WannaBAcoder/ArenaTimer/STLs/TimerPrints/Multi-Piece Housing/Bottom_right.stl

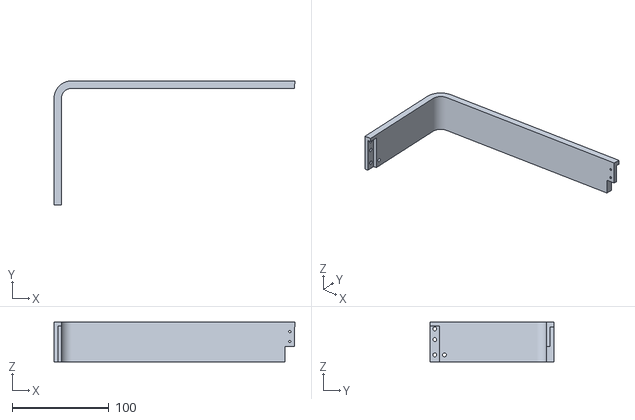
[picture p17: CAD file, 2026-06-10]
STLs/TimerPrints/Multi-Piece Housing/Bottom_right.stl
248.6 x 128.0 x 41.0
