WannaBAcoder/ArenaTimer/STLs/TimerPrints/Multi-Piece Housing/Lenses/seg_a.stl

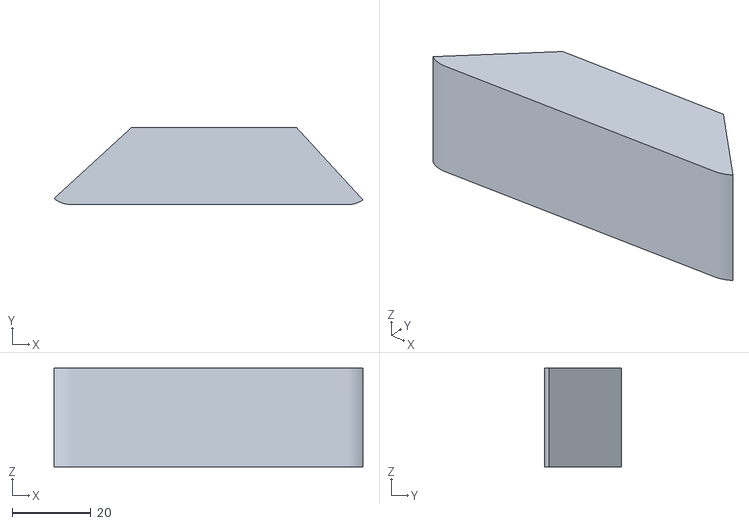
[picture p18: CAD file, 2026-06-10]
STLs/TimerPrints/Multi-Piece Housing/Lenses/seg_a.stl
78.4 x 19.6 x 25.0
