WannaBAcoder/ArenaTimer/STLs/TimerPrints/Single Piece Housing/Lenses/seg_a.stl

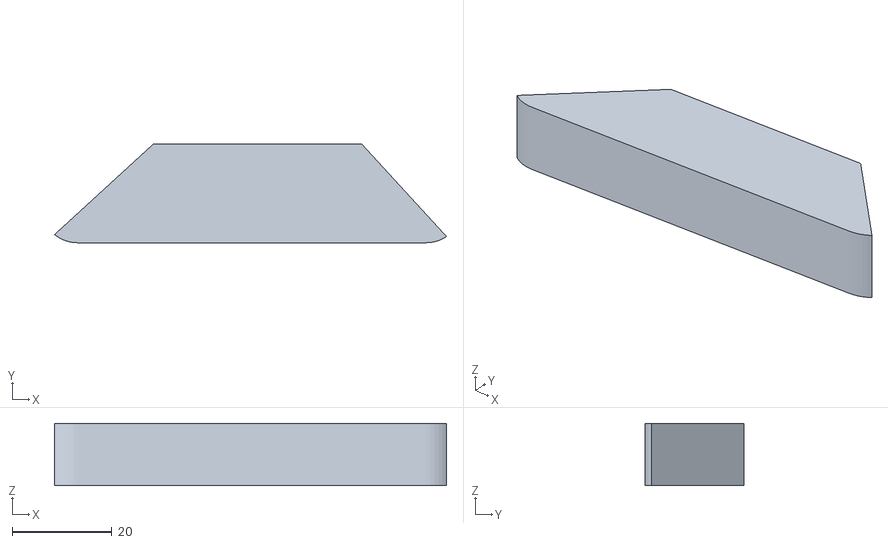
[picture p19: CAD file, 2026-06-10]
STLs/TimerPrints/Single Piece Housing/Lenses/seg_a.stl
78.7 x 19.8 x 12.5
