WannaBAcoder/ArenaTimer/STLs/TimerPrints/Button Cases/ControllerHousing/ControllerHousing_ButtonBoard v22_Body4.stl

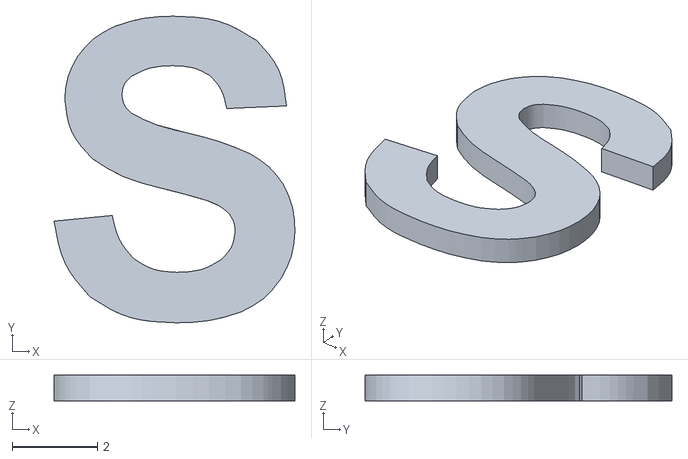
[picture p20: CAD file, 2026-06-10]
STLs/TimerPrints/Button Cases/ControllerHousing/ControllerHousing_ButtonBoard v22_Body4.stl
5.65 x 7.18 x 0.6
