WannaBAcoder/ArenaTimer/STLs/TimerPrints/Button Cases/ReadyButtonHousing/ReadyButtonHousing_LargerReadyButton v7_Body14.stl

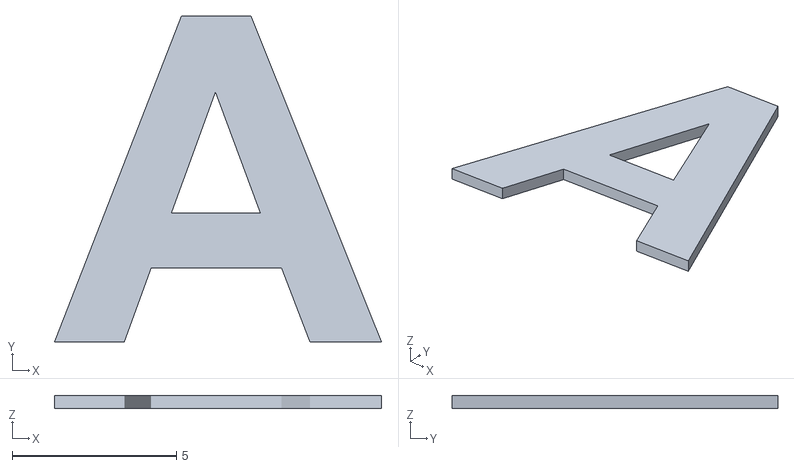
[picture p21: CAD file, 2026-06-10]
STLs/TimerPrints/Button Cases/ReadyButtonHousing/ReadyButtonHousing_LargerReadyButton v7_Body14.stl
9.95 x 9.92 x 0.4
