WannaBAcoder/ArenaTimer/STLs/TimerPrints/Multi-Piece Housing/Top_right.stl

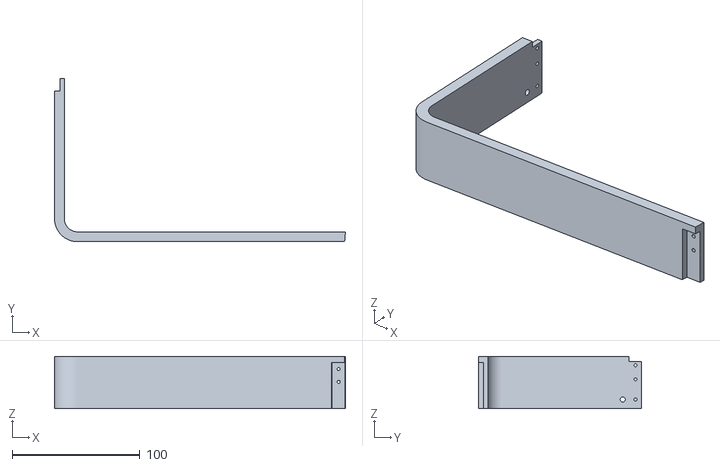
[picture p22: CAD file, 2026-06-10]
STLs/TimerPrints/Multi-Piece Housing/Top_right.stl
227.7 x 127.8 x 41.0
