WannaBAcoder/ArenaTimer/STLs/TimerPrints/Single Piece Housing/Lenses/seg_b.stl

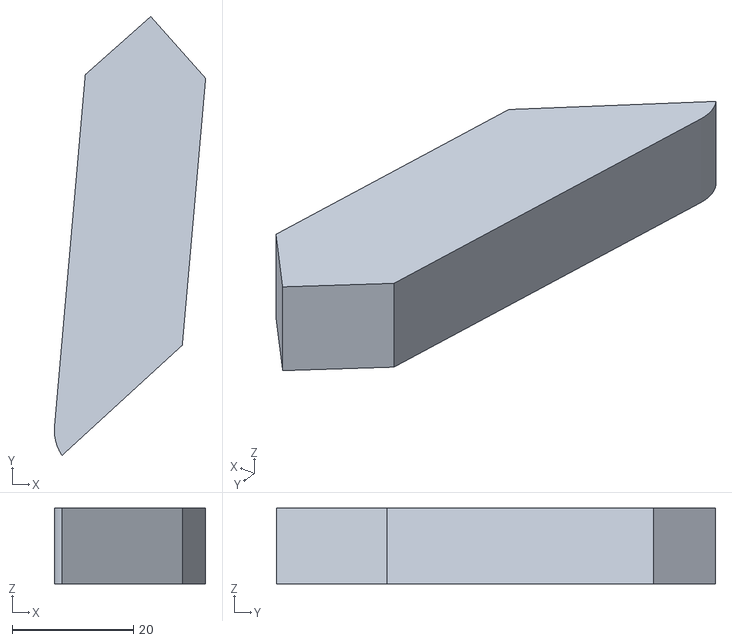
[picture p23: CAD file, 2026-06-10]
STLs/TimerPrints/Single Piece Housing/Lenses/seg_b.stl
24.9 x 72.3 x 12.5
