WannaBAcoder/ArenaTimer/STLs/TimerPrints/Button Cases/ReadyButtonHousing/ReadyButtonHousing_LargerReadyButton v7_Body17.stl

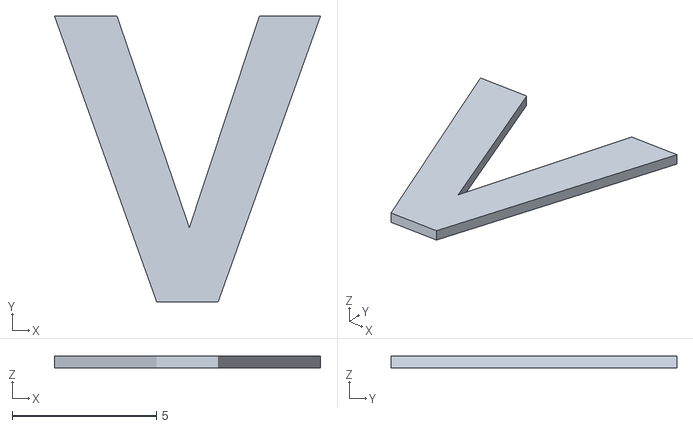
[picture p24: CAD file, 2026-06-10]
STLs/TimerPrints/Button Cases/ReadyButtonHousing/ReadyButtonHousing_LargerReadyButton v7_Body17.stl
9.24 x 9.92 x 0.4
