WannaBAcoder/ArenaTimer/STLs/TimerPrints/Multi-Piece Housing/Bottom_left.stl

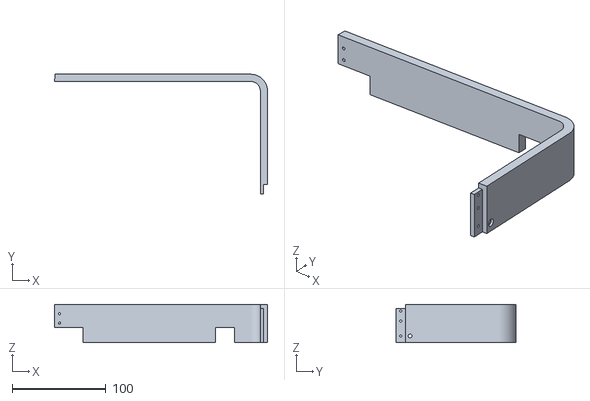
[picture p25: CAD file, 2026-06-10]
STLs/TimerPrints/Multi-Piece Housing/Bottom_left.stl
227.7 x 127.8 x 41.0
