WannaBAcoder/ArenaTimer/STLs/TimerPrints/Multi-Piece Housing/Lenses/Colon_lens.stl

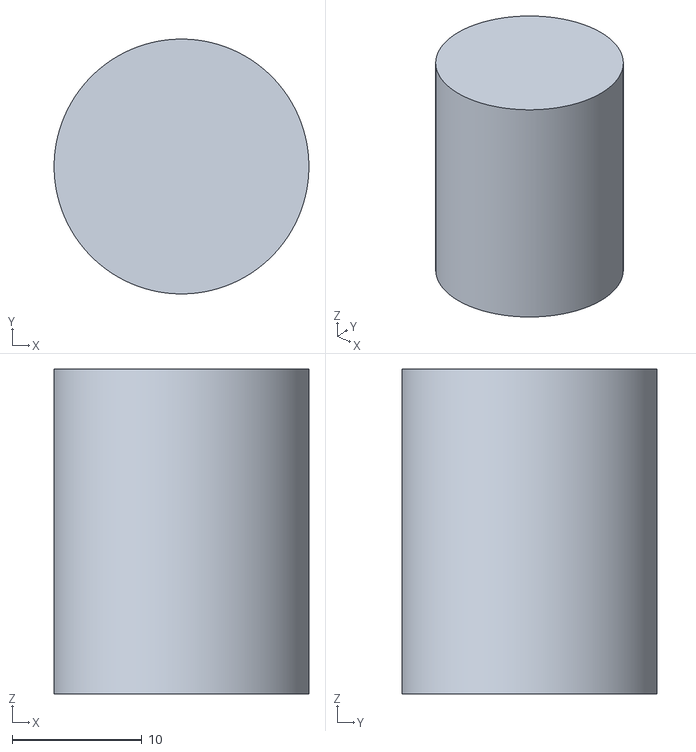
[picture p26: CAD file, 2026-06-10]
STLs/TimerPrints/Multi-Piece Housing/Lenses/Colon_lens.stl
19.6 x 19.6 x 25.0
