WannaBAcoder/ArenaTimer/STLs/TimerPrints/Single Piece Housing/Lenses/colon.stl

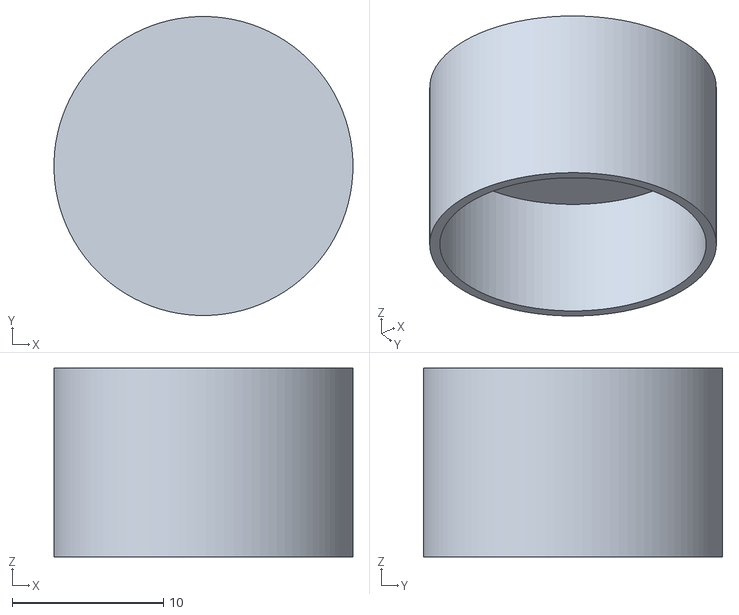
[picture p27: CAD file, 2026-06-10]
STLs/TimerPrints/Single Piece Housing/Lenses/colon.stl
19.8 x 19.8 x 12.5
