WannaBAcoder/ArenaTimer/STLs/TimerPrints/Button Cases/ReadyButtonHousing/ReadyButtonHousing_LargerReadyButton v7_shell.stl

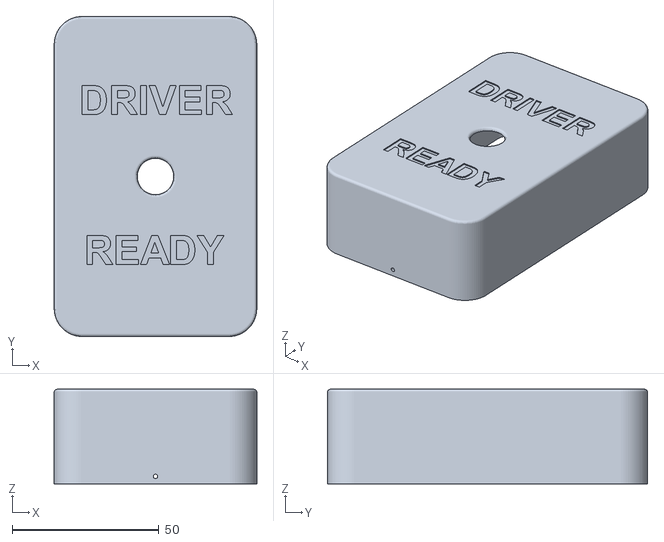
[picture p28: CAD file, 2026-06-10]
STLs/TimerPrints/Button Cases/ReadyButtonHousing/ReadyButtonHousing_LargerReadyButton v7_shell.stl
69.0 x 109.0 x 32.2
