WannaBAcoder/ArenaTimer/STLs/TimerPrints/Multi-Piece Housing/Lenses/seg_e.stl

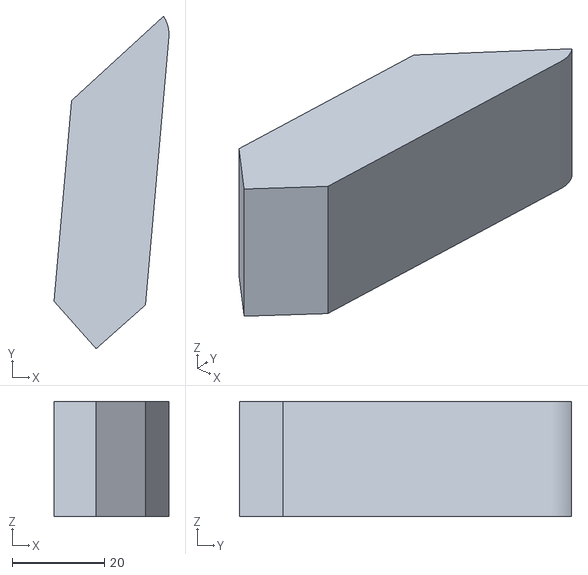
[picture p29: CAD file, 2026-06-10]
STLs/TimerPrints/Multi-Piece Housing/Lenses/seg_e.stl
24.9 x 72.0 x 25.0
