WannaBAcoder/ArenaTimer/STLs/TimerPrints/Button Cases/ControllerHousing/ControllerHousing_ButtonBoard v22_Body3.stl

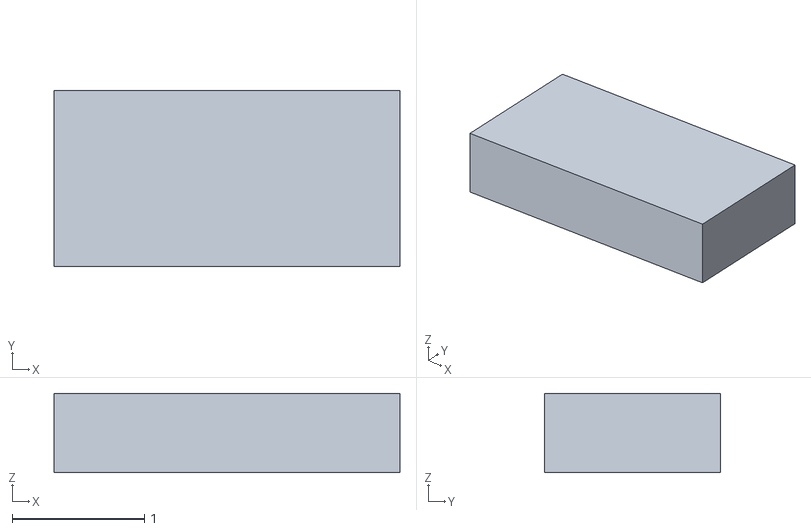
[picture p30: CAD file, 2026-06-10]
STLs/TimerPrints/Button Cases/ControllerHousing/ControllerHousing_ButtonBoard v22_Body3.stl
2.61 x 1.33 x 0.6
