WannaBAcoder/ArenaTimer/STLs/TimerPrints/Button Cases/ReadyButtonHousing/ReadyButtonHousing_LargerReadyButton v7_Body16.stl

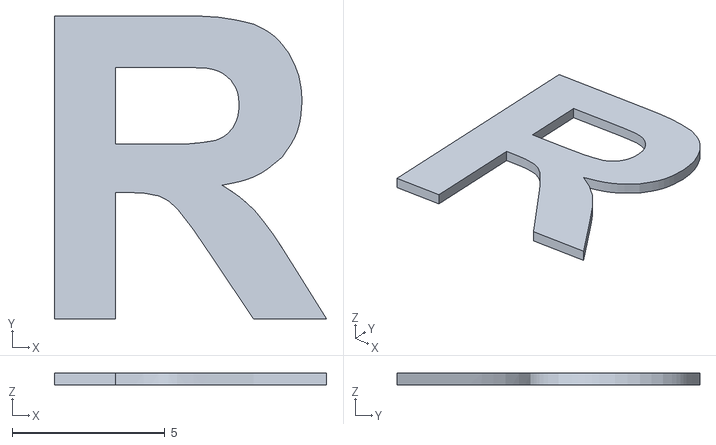
[picture p31: CAD file, 2026-06-10]
STLs/TimerPrints/Button Cases/ReadyButtonHousing/ReadyButtonHousing_LargerReadyButton v7_Body16.stl
8.92 x 9.92 x 0.4
