WannaBAcoder/ArenaTimer/STLs/TimerPrints/Button Cases/ControllerHousing/ControllerHousing_ButtonBoard v22_Body21.stl

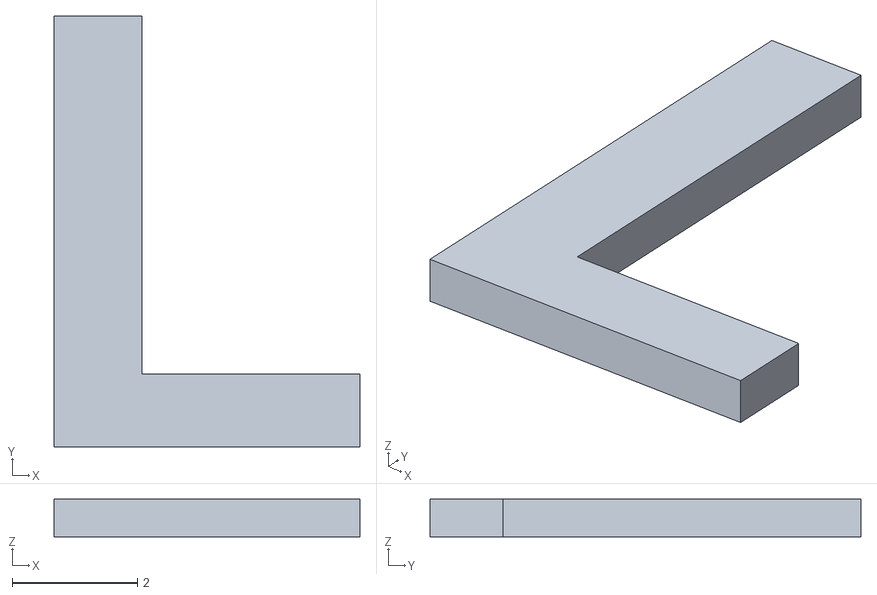
[picture p32: CAD file, 2026-06-10]
STLs/TimerPrints/Button Cases/ControllerHousing/ControllerHousing_ButtonBoard v22_Body21.stl
4.89 x 6.89 x 0.6
