WannaBAcoder/ArenaTimer/STLs/TimerPrints/Single Piece Housing/Lenses/seg_g.stl

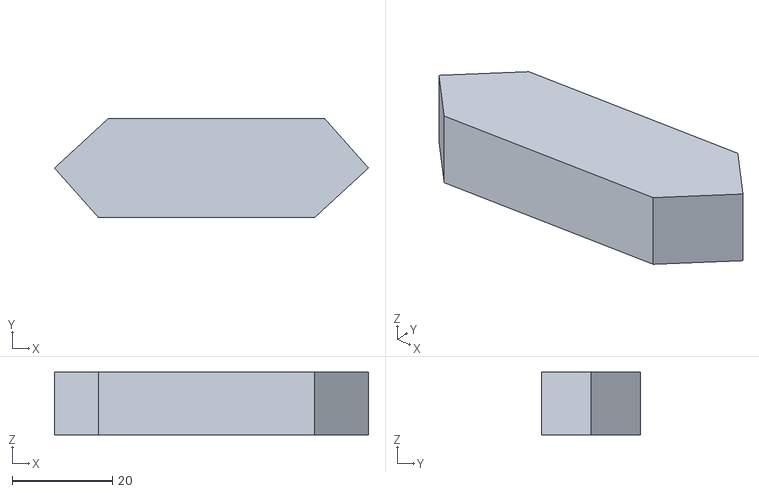
[picture p33: CAD file, 2026-06-10]
STLs/TimerPrints/Single Piece Housing/Lenses/seg_g.stl
62.6 x 19.8 x 12.5
