WannaBAcoder/ArenaTimer/STLs/TimerPrints/Button Cases/ControllerHousing/ControllerHousing_ButtonBoard v22_Body8.stl

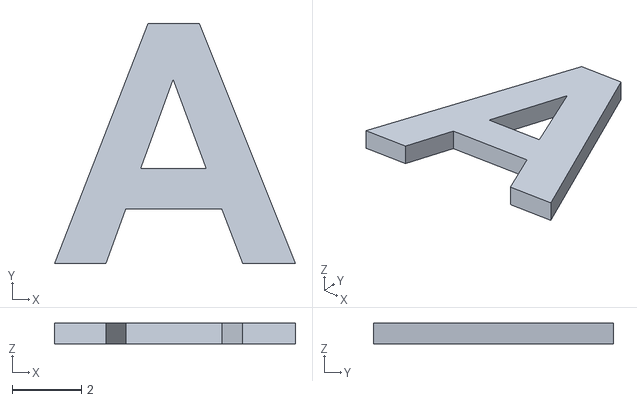
[picture p34: CAD file, 2026-06-10]
STLs/TimerPrints/Button Cases/ControllerHousing/ControllerHousing_ButtonBoard v22_Body8.stl
6.97 x 6.94 x 0.6
