WannaBAcoder/ArenaTimer/STLs/TimerPrints/Button Cases/ControllerHousing/ControllerHousing_ButtonBoard v22_Body9.stl

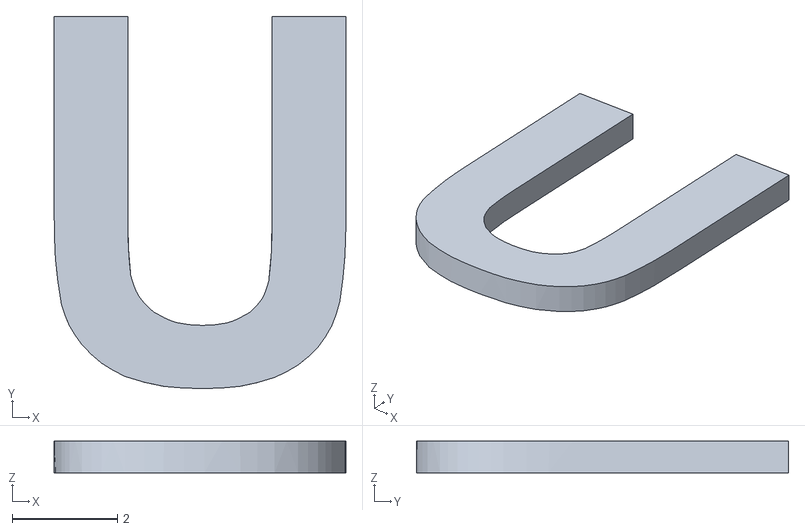
[picture p35: CAD file, 2026-06-10]
STLs/TimerPrints/Button Cases/ControllerHousing/ControllerHousing_ButtonBoard v22_Body9.stl
5.54 x 7.06 x 0.6
