WannaBAcoder/ArenaTimer/STLs/TimerPrints/Button Cases/ReadyButtonHousing/ReadyButtonHousing_LargerReadyButton v7_Body9.stl

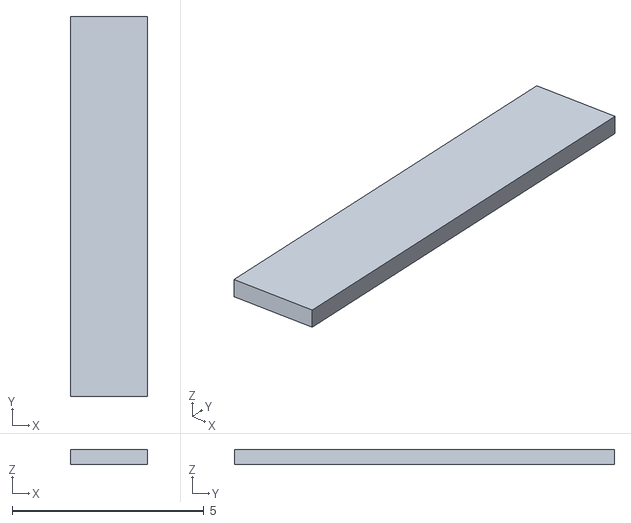
[picture p36: CAD file, 2026-06-10]
STLs/TimerPrints/Button Cases/ReadyButtonHousing/ReadyButtonHousing_LargerReadyButton v7_Body9.stl
2.00 x 9.92 x 0.4
