WannaBAcoder/ArenaTimer/STLs/TimerPrints/Multi-Piece Housing/Lenses/seg_b.stl

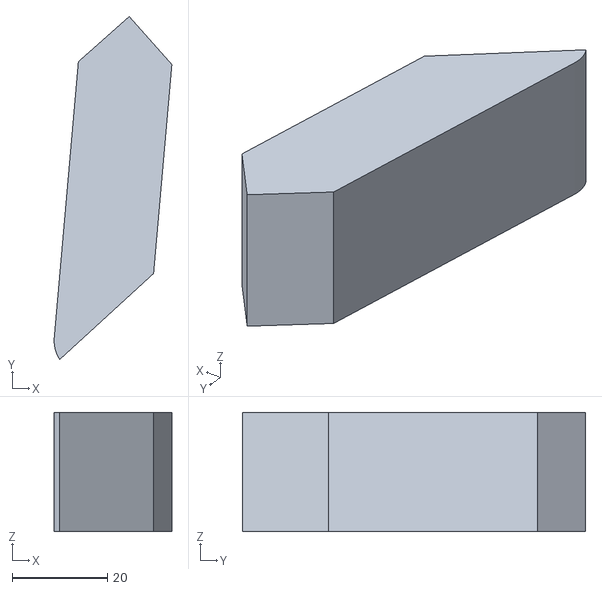
[picture p37: CAD file, 2026-06-10]
STLs/TimerPrints/Multi-Piece Housing/Lenses/seg_b.stl
24.7 x 72.0 x 25.0
