WannaBAcoder/ArenaTimer/STLs/TimerPrints/Multi-Piece Housing/Lenses/seg_g.stl

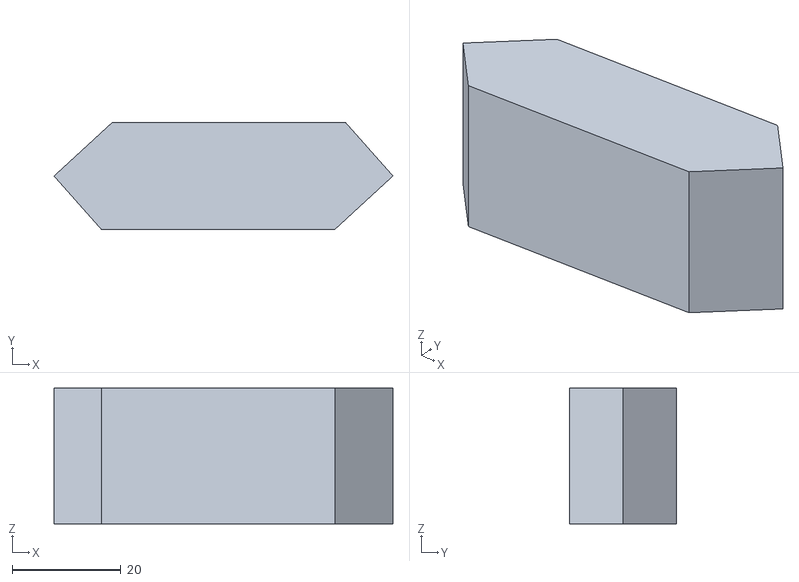
[picture p40: CAD file, 2026-06-10]
STLs/TimerPrints/Multi-Piece Housing/Lenses/seg_g.stl
62.4 x 19.6 x 25.0
